hardwareliberopinerolo/CantaStorie/00_Arduino_Sketches/CS_Random_R03/_500_setup_f.ino

// ---- SETUP -----------------
void setup(){
  Serial.begin(115200);
  Serial.setTimeout(2000);
  Serial.println(F("initializing..."));
  

  pinMode(MP3_busy,OUTPUT);
  pinMode(LED1,OUTPUT);
  pinMode(LED2,OUTPUT);
  digitalWrite(LED1,LOW);
  digitalWrite(LED2,LOW);
  
  ezprom.setOverwriteIfSizeDifferent(true);
  read_eeprom();
  delay(100);
  
  mp3.begin();
  delay(50); 
  mp3.stop(); // stop
  //mp3.setVolume(0);
  mp3.setVolume(volume);
  delay(50);
  uint16_t volume = mp3.getVolume();
  Serial.print(F("volume "));
  Serial.println(volume);
  uint16_t count = mp3.getTotalTrackCount();
  Serial.print(F("files "));
  Serial.println(count);
  Serial.println(F("starting..."));
  SPI.begin(); // Init SPI bus
  rfid.PCD_Init(); // Init MFRC522 


randomSeed(analogRead(0));

  /*
  mp3.reset();
  mp3.setVolume(10);
  mp3.setVolume(--volume);
  delay(100);
  mp3.setVolume(++volume);
  delay(100);
  */
  Serial.println(F("Waiting for an RFID card"));
}
