hardwareliberopinerolo/CantaStorie/00_Arduino_Sketches/CS_Random_R03/_900_commenti.ino

/* NOTES
 *  Avvio 
 *  in void setup()
 *    read_eeprom(); legge i parametri in EEEPROM interna
 *    con la funzione ezprom.load(uide_id, **uid_ok);
 *    uide è la posizione iniziale in EEPROM, iniza la zona 
 *        dove sono archiviati UID delle schede  
 *    uid_ok è un array bidimensionale dove vengono posizionati    
 *        posizione evalore dell'UID della scheda


Libreria MP3
https://github.com/Makuna/DFMiniMp3


Libreria RFID RC522
https://github.com/miguelbalboa/rfid


Libreria Ezprom
https://github.com/amirchev/EZPROM



Per resettare la memoria Eeprom premere R nel serial monitor e poi fare acquisizione carte




 */
